DreaM117er/Vanguard-Keyboard-Outsider/file/pcb/generic/TPS-unit4/TPS.kicad_sch

## KiCad design file/pcb/generic/TPS-unit4/TPS.kicad_sch (2026-05-12)

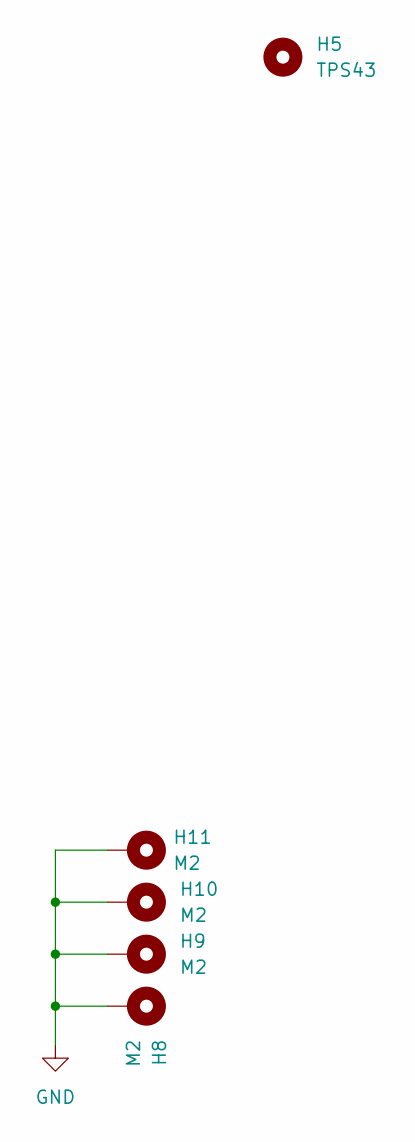
[picture p93: schematic TPS.kicad_sch]

Parts:
H5: TPS43; Azoteq_TPS43_201A_S
H8, H9, H10, H11: M2; MountingHole_2.2mm_M2_Nut_THT

Connections:
GND: H8.1, H9.1, H10.1, H11.1
