DreaM117er/Vanguard-Keyboard-Outsider/file/pcb/v1/case/outsider.kicad_sch

## KiCad design file/pcb/v1/case/outsider.kicad_sch (2026-05-12)

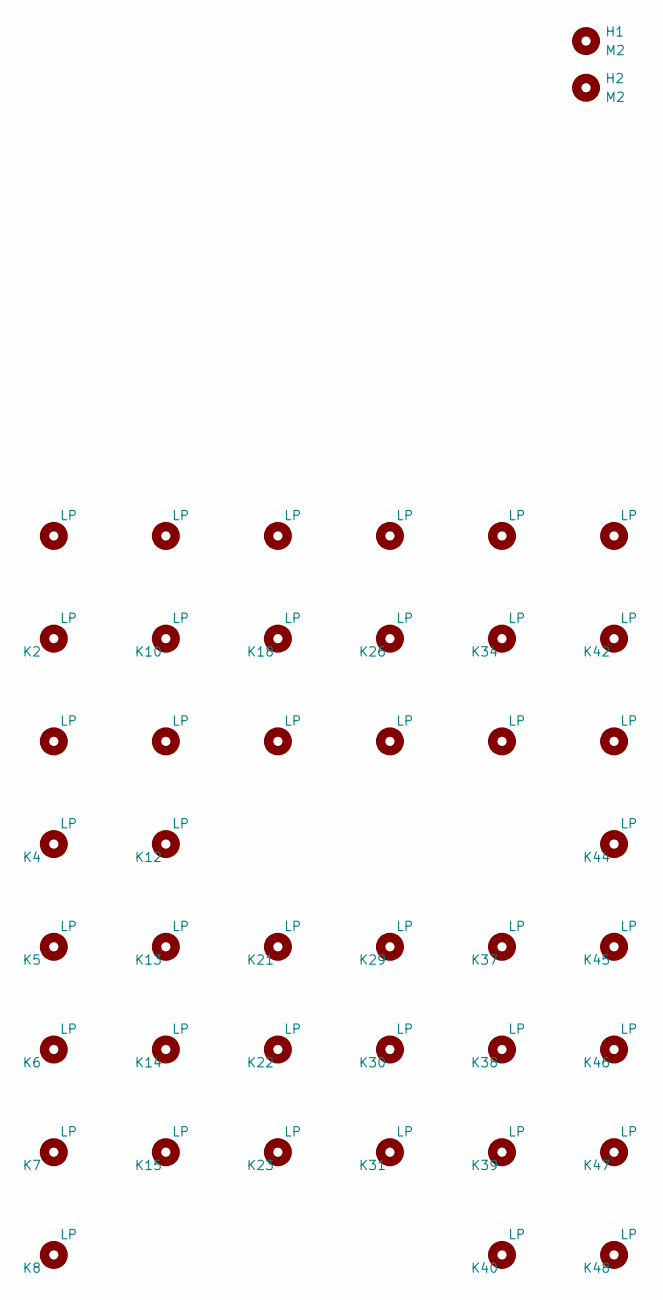
[picture p94: schematic outsider.kicad_sch]

Parts:
H1, H2: M2; MountingHole_2.2mm_M2_Nut
K1, K2, K3, K4, K5, K6, K7, K8, K9, K10, K11, K12, K13, K14, K15, K17, K18, K19, K21, K22, K23, K25, K26, K27, K29, K30, K31, K33, K34, K35, K37, K38, K39, K40, K41, K42, K43, K44, K45, K46, K47, K48: LP; SW_Keyboard_Hole_1.00u
