DreaM117er/Vanguard-Keyboard-Outsider/file/pcb/v1/pcb/outsider.kicad_sch

## KiCad design file/pcb/v1/pcb/outsider.kicad_sch (2026-05-11)

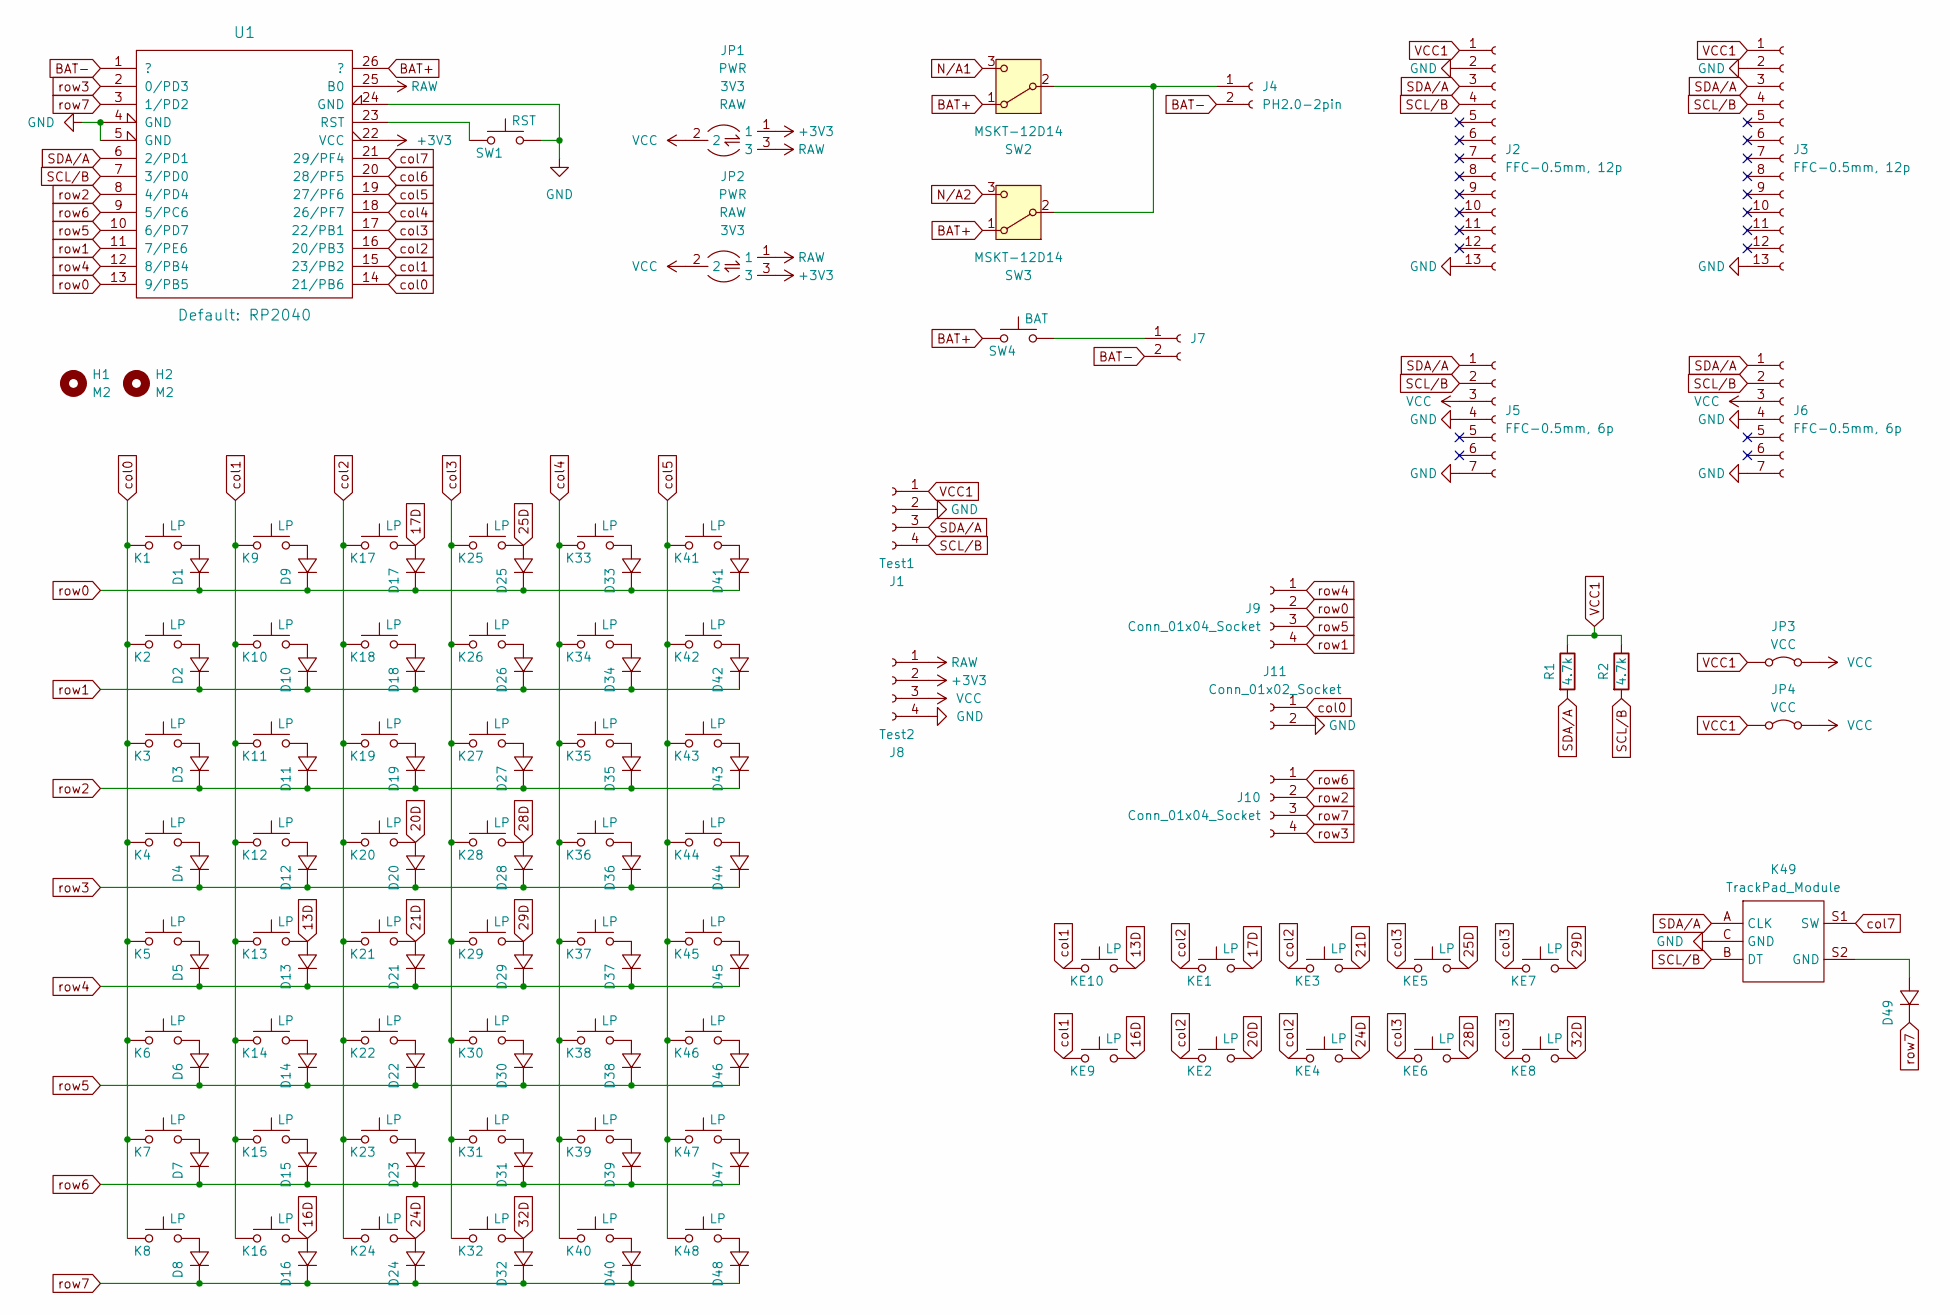
[picture p95: schematic outsider.kicad_sch]

Parts:
D1, D2, D3, D4, D5, D6, D7, D8, D9, D10, D11, D12, D13, D14, D15, D16, D17, D18, D19, D20, D21, D22, D23, D24, D25, D26, D27, D28, D29, D30, D31, D32, D33, D34, D35, D36, D37, D38, D39, D40, D41, D42, D43, D44, D45, D46, D47, D48, D49: 1N4148_SMD; D_SOD-123_handsolder_dual
H1, H2: M2; MountingHole_2.2mm_M2_Nut
J1: Test1; PinHeader_1x04_P2.54mm_Vertical
J2, J3: FFC-0.5mm, 12p; Hirose_FH12-12S-0.5SH_1x12-1MP_P0.50mm_Horizontal
J4: PH2.0-2pin; JST_PH_S2B-PH-K_1x02_P2.00mm_Horizontal_dual
J5, J6: FFC-0.5mm, 6p; Hirose_FH12-6S-0.5SH_1x06-1MP_P0.50mm_Horizontal
J7: PinHeader_1x02_P2.54mm_Vertical
J8: Test2; PinHeader_1x04_P2.54mm_Vertical
J9, J10: Conn_01x04_Socket; PinHeader_1x04_P2.54mm_Vertical
J11: Conn_01x02_Socket; PinHeader_1x02_P2.54mm_Vertical
JP1, JP2: PWR; Jumper_1-3_SingleSide
JP3, JP4: VCC; SolderJumper-2_P1.3mm_Open_RoundedPad1.0x1.5mm
K1, K2, K3, K4, K5, K6, K7, K8, K9, K10, K11, K12, K13, K14, K15, K16, K17, K18, K19, K20, K21, K22, K23, K24, K25, K26, K27, K28, K29, K30, K31, K32, K33, K34, K35, K36, K37, K38, K39, K40, K41, K42, K43, K44, K45, K46, K47, K48: LP; SW_KLP12_GLP3.0_MX_1.00u_dual_oneside3
K49: TrackPad_Module; Explorerkb_Trackpad_Module_with_EC11
KE1, KE2, KE3, KE4, KE5, KE6, KE7, KE8, KE9, KE10: LP; SW_KLP12_GLP3.0_MX_1.00u_dual_oneside3
R1, R2: 4.7k; R_Axial_DIN0204_L3.6mm_D1.6mm_P7.62mm_Horizontal
SW1: RST; ResetSW_1side
SW2, SW3: MSKT-12D14; SW_SPDT_MSKT-12D14_SMD_dual
SW4: BAT; SW_Push_SPST_NO_Alps_SKRK_handsolder_dual
U1: Default: RP2040; MCU_ProMicro_13p_dual_3rd

Connections:
13D: D13.2, K13.2, KE10.2
16D: D16.2, K16.2, KE9.2
17D: D17.2, K17.2, KE1.2
20D: D20.2, K20.2, KE2.2
21D: D21.2, K21.2, KE3.2
24D: D24.2, K24.2, KE4.2
25D: D25.2, K25.2, KE5.2
28D: D28.2, K28.2, KE6.2
29D: D29.2, K29.2, KE7.2
32D: D32.2, K32.2, KE8.2
+3V3: J8.2, JP1.1, JP2.3, U1.22 (VCC)
BAT+: SW2.1 (A), SW3.1 (A), SW4.1, U1.26 (?)
BAT-: J4.2, J7.2, U1.1 (?)
GND: J1.2, J2.2, J2.13, J3.2, J3.13, J5.4, J5.7, J6.4, J6.7, J8.4, J11.2, K49.C (GND), SW1.2, U1.4 (GND), U1.5 (GND), U1.24 (GND)
unnamed: D1.2, K1.2
unnamed: D2.2, K2.2
unnamed: D3.2, K3.2
unnamed: D4.2, K4.2
unnamed: D5.2, K5.2
unnamed: D6.2, K6.2
unnamed: D7.2, K7.2
unnamed: D8.2, K8.2
unnamed: D9.2, K9.2
unnamed: D10.2, K10.2
unnamed: D11.2, K11.2
unnamed: D12.2, K12.2
unnamed: D14.2, K14.2
unnamed: D15.2, K15.2
unnamed: D18.2, K18.2
unnamed: D19.2, K19.2
unnamed: D22.2, K22.2
unnamed: D23.2, K23.2
unnamed: D26.2, K26.2
unnamed: D27.2, K27.2
unnamed: D30.2, K30.2
unnamed: D31.2, K31.2
unnamed: D33.2, K33.2
unnamed: D34.2, K34.2
unnamed: D35.2, K35.2
unnamed: D36.2, K36.2
unnamed: D37.2, K37.2
unnamed: D38.2, K38.2
unnamed: D39.2, K39.2
unnamed: D40.2, K40.2
unnamed: D41.2, K41.2
unnamed: D42.2, K42.2
unnamed: D43.2, K43.2
unnamed: D44.2, K44.2
unnamed: D45.2, K45.2
unnamed: D46.2, K46.2
unnamed: D47.2, K47.2
unnamed: D48.2, K48.2
unnamed: D49.2, K49.S2 (GND)
unnamed: J4.1, SW2.2 (B), SW3.2 (B)
unnamed: J7.1, SW4.2
unnamed: SW1.1, U1.23 (RST)
N/A1: SW2.3 (C)
N/A2: SW3.3 (C)
RAW: J8.1, JP1.3, JP2.1, U1.25 (B0)
SCL/B: J1.4, J2.4, J3.4, J5.2, J6.2, K49.B (DT), R2.2, U1.7 (3/PD0)
SDA/A: J1.3, J2.3, J3.3, J5.1, J6.1, K49.A (CLK), R1.2, U1.6 (2/PD1)
VCC: J5.3, J6.3, J8.3, JP1.2, JP2.2, JP3.2 (B), JP4.2 (B)
VCC1: J1.1, J2.1, J3.1, JP3.1 (A), JP4.1 (A), R1.1, R2.1
col0: J11.1, K1.1, K2.1, K3.1, K4.1, K5.1, K6.1, K7.1, K8.1, U1.14 (21/PB6)
col1: K9.1, K10.1, K11.1, K12.1, K13.1, K14.1, K15.1, K16.1, KE9.1, KE10.1, U1.15 (23/PB2)
col2: K17.1, K18.1, K19.1, K20.1, K21.1, K22.1, K23.1, K24.1, KE1.1, KE2.1, KE3.1, KE4.1, U1.16 (20/PB3)
col3: K25.1, K26.1, K27.1, K28.1, K29.1, K30.1, K31.1, K32.1, KE5.1, KE6.1, KE7.1, KE8.1, U1.17 (22/PB1)
col4: K33.1, K34.1, K35.1, K36.1, K37.1, K38.1, K39.1, K40.1, U1.18 (26/PF7)
col5: K41.1, K42.1, K43.1, K44.1, K45.1, K46.1, K47.1, K48.1, U1.19 (27/PF6)
col6: U1.20 (28/PF5)
col7: K49.S1 (SW), U1.21 (29/PF4)
row0: D1.1, D9.1, D17.1, D25.1, D33.1, D41.1, J9.2, U1.13 (9/PB5)
row1: D2.1, D10.1, D18.1, D26.1, D34.1, D42.1, J9.4, U1.11 (7/PE6)
row2: D3.1, D11.1, D19.1, D27.1, D35.1, D43.1, J10.2, U1.8 (4/PD4)
row3: D4.1, D12.1, D20.1, D28.1, D36.1, D44.1, J10.4, U1.2 (0/PD3)
row4: D5.1, D13.1, D21.1, D29.1, D37.1, D45.1, J9.1, U1.12 (8/PB4)
row5: D6.1, D14.1, D22.1, D30.1, D38.1, D46.1, J9.3, U1.10 (6/PD7)
row6: D7.1, D15.1, D23.1, D31.1, D39.1, D47.1, J10.1, U1.9 (5/PC6)
row7: D8.1, D16.1, D24.1, D32.1, D40.1, D48.1, D49.1, J10.3, U1.3 (1/PD2)
